icrnjavic/ArduDAQ/docs/pictures/2.png

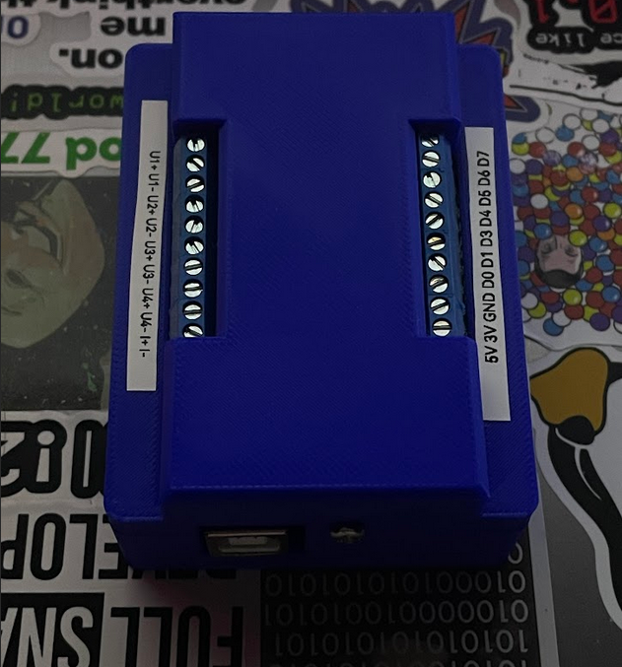
docs/pictures/2.png
