icrnjavic/ArduDAQ/docs/pictures/real-world-example.png

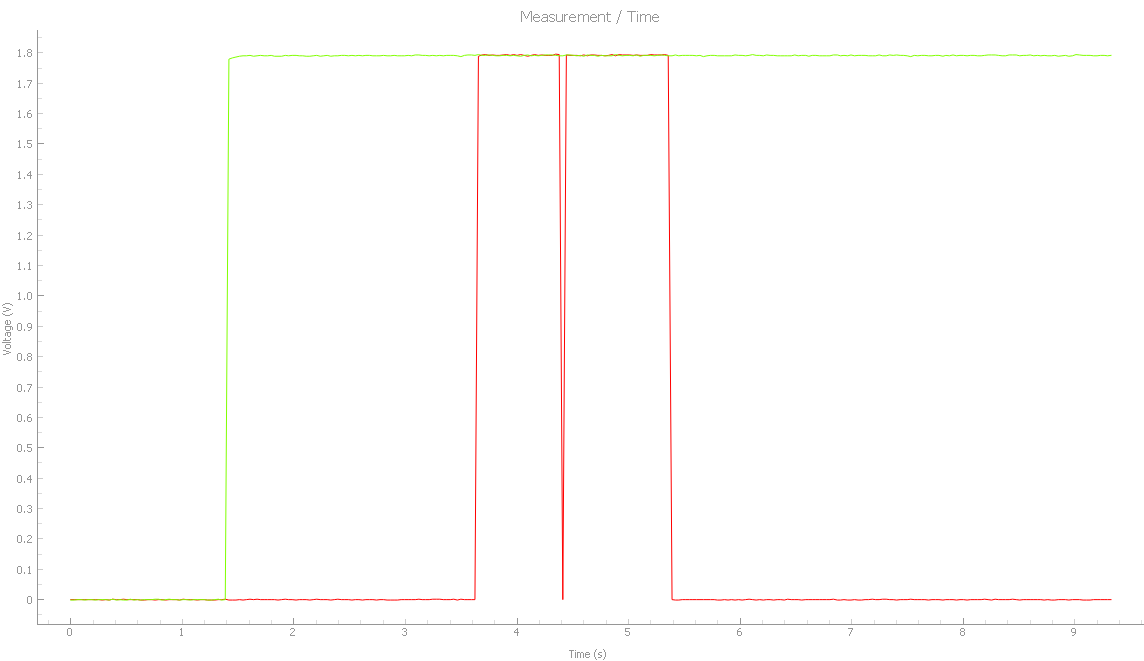
docs/pictures/real-world-example.png
