icrnjavic/ArduDAQ/docs/pictures/accuracy_test.png

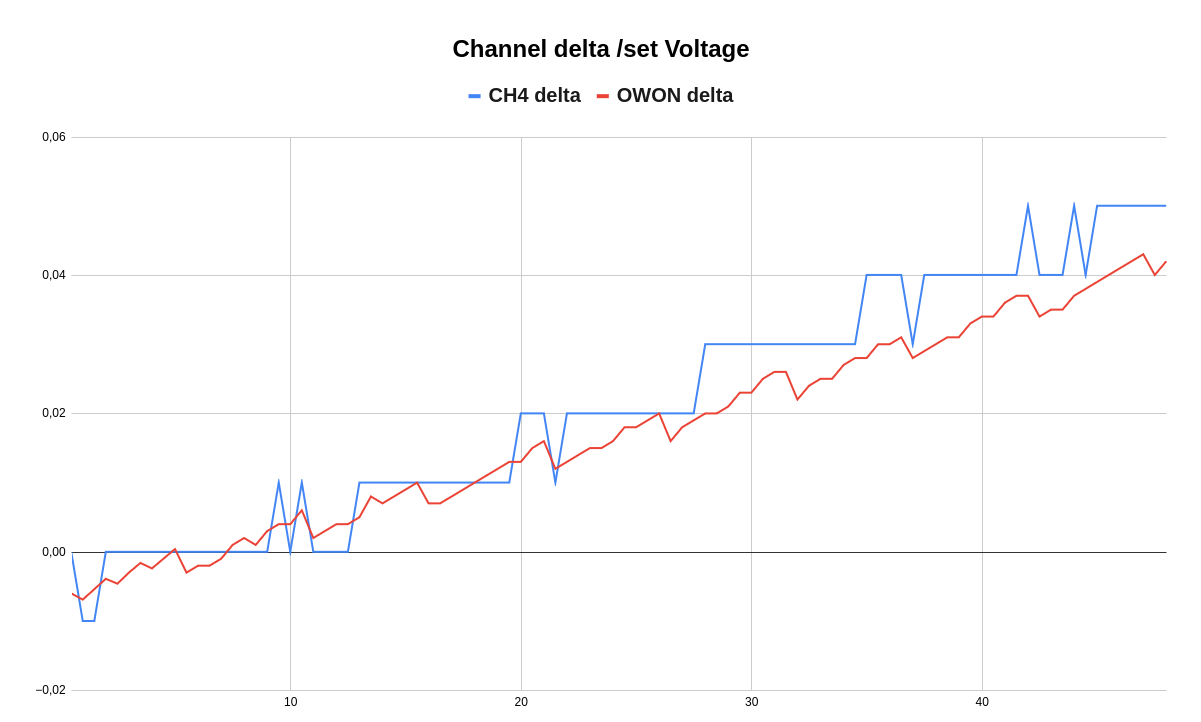
docs/pictures/accuracy_test.png
